ErfanRht/Analog-Voltage-Multiplier-Circuit/images/photo_2025-09-12_16-41-55.jpg

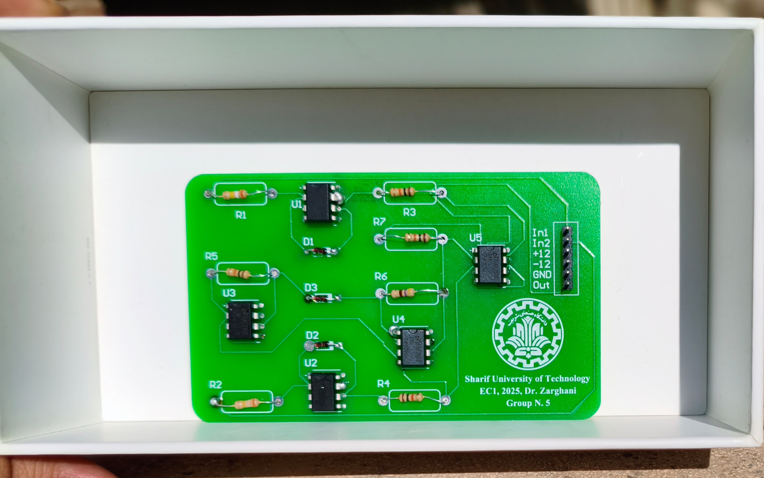
images/photo_2025-09-12_16-41-55.jpg
