ErfanRht/Analog-Voltage-Multiplier-Circuit/LtSpice - Schematic.asc

D1: diode; 1N4148
D2: diode; 1N4148
D3: diode; 1N4148
R1: res; {Rf}
R2: res; {Ri}
R3: res; {Rf}
R4: res; {Rs}
R5: res; {Rs}
R6: res; {Rs}
R7: res; {Rs}
R8: res; {Rs}
U1: LM741
U2: LM741
U3: LM741
U4: LM741
U5: LM741
V1: voltage; 12Vdc
V2: voltage; -12Vdc
V3: voltage; 1.4
V4: voltage; 1.3
Named nets: 0, Vcc+, Vcc-, Vin2, Vin1, Vout
.tran 0.1
.param Rf 410k
.param Ri 0.470k
.param Rs 10k
